timotei-iosif/proiect-tsc/Hardware/tsc.sch

## EAGLE design Hardware/tsc.sch (2026-04-10)

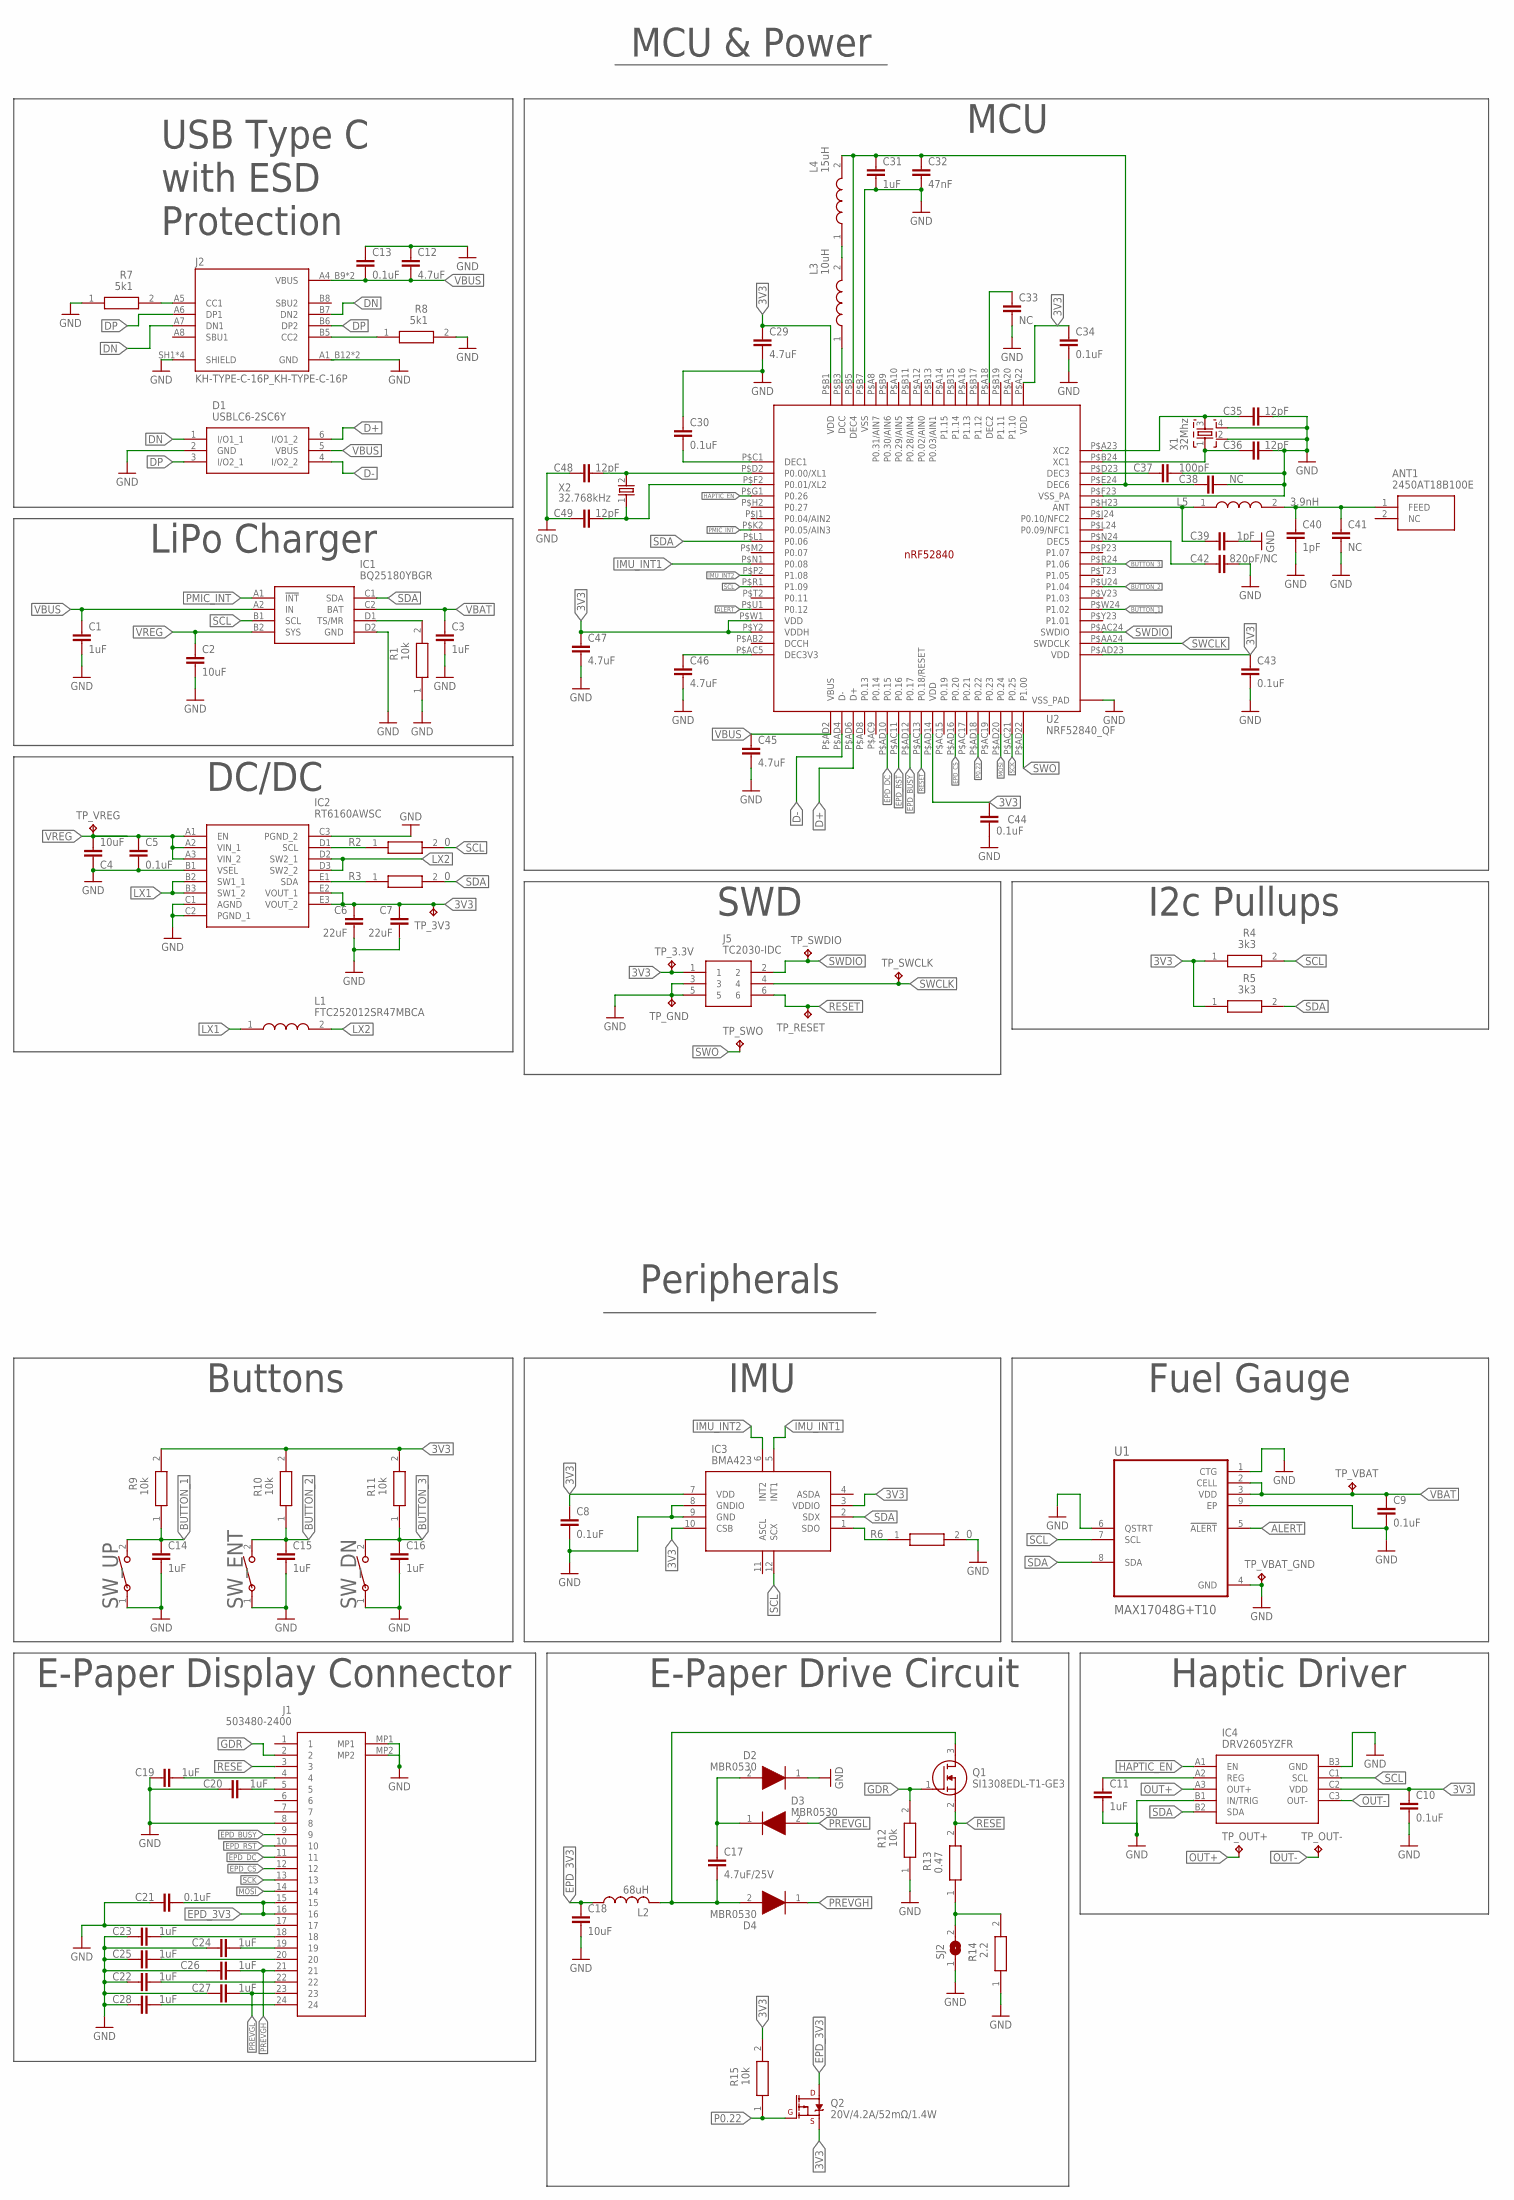
[picture p4: schematic tsc.sch]

Parts:
ANT1: 2450AT18B100E; 2450AT18B100E_ANTC3216X140N
C1, C3, C11, C14, C15, C16, C19, C20, C22, C23, C24, C25, C26, C27, C28, C31: 1uF; NORDIC_NRF_3_RESC0402_N
C2, C4, C18: 10uF; NORDIC_NRF_3_RESC0402_N
C5, C8, C9, C10, C13, C21, C30, C34, C43, C44: 0.1uF; NORDIC_NRF_3_RESC0201_N
C6, C7: 22uF; NORDIC_NRF_3_RESC0402_N
C12, C29, C45, C46, C47: 4.7uF; NORDIC_NRF_3_RESC0402_N
C17: 4.7uF/25V; NORDIC_NRF_3_RESC0402_N
C32: 47nF; NORDIC_NRF_3_RESC0201_N
C33, C38, C41: NC; NORDIC_NRF_3_RESC0201_N
C35, C36, C48, C49: 12pF; NORDIC_NRF_3_RESC0201_N
C37: 100pF; NORDIC_NRF_3_RESC0201_N
C39, C40: 1pF; NORDIC_NRF_3_RESC0201_N
C42: 820pF/NC; NORDIC_NRF_3_RESC0201_N
D1: USBLC6-2SC6Y; ESP32_C6_LIBRARY_3_SOT95P280X145-6N
D2, D3, D4: MBR0530; ESP32_C6_LIBRARY_5_SOD3716X135N
IC1: BQ25180YBGR; BQ25180YBGR_BGA8C40P2X4_100X155X50
IC2: RT6160AWSC; RT6160AWSC_BGA15C40P3X5_140X230X60
IC3: BMA423; BMA423_BMA423
IC4: DRV2605YZFR; DRV2605YZFR_BGA9C50P3X3_144X144X62
J1: 503480-2400; 503480-2400_5034802400
J2: KH-TYPE-C-16P_KH-TYPE-C-16P; KH-TYPE-C-16P_KINGHELM_KH-TYPE-C-16P
J5: TC2030-IDC; TC2030-IDC_TC2030IDC
L1: FTC252012SR47MBCA; MLP2016SR47MT0S1_INDC2016X100N
L2: 68uH; NORDIC_NRF_2_RESC0402_L
L3: 10uH; MLP2016SR47MT0S1_INDC2016X100N
L4: 15uH; MLP2016SR47MT0S1_INDC2016X100N
L5: 3.9nH; MLP2016SR47MT0S1_INDC2016X100N
Q1: SI1308EDL-T1-GE3; ESP32_C6_LIBRARY_6_SOT65P210X110-3N
Q2: 20V/4.2A/52mΩ/1.4W; ESP32_C6_LIBRARY_4_ESP32_C6_LIBRARY_4_ESP32_C6_LIBRARY_4_ES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
R1, R9, R10, R11, R12, R15: 10k; CPF0201D7K68C1_0201
R2, R3, R6: 0; CPF0201D7K68C1_0201
R4, R5: 3k3; CPF0201D7K68C1_0201
R7, R8: 5k1; CPF0201D7K68C1_0201
R13: 0.47; CPF0201D7K68C1_0201
R14: 2.2; CPF0201D7K68C1_0201
SJ2: -; ESP32_C6_LIBRARY_7_JUMPER_SJ
SW_DN: 2025-10-22_07-23-44_LIBRARY_EVP-AKE31ASW_EVP-AKE3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; 2025-10-22_07-23-44_LIBRARY_SW_EVP-AKE31A_PAN
SW_ENT: 2025-10-22_07-23-44_LIBRARY_EVP-AKE31ASW_EVP-AKE3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; 2025-10-22_07-23-44_LIBRARY_SW_EVP-AKE31A_PAN
SW_UP: 2025-10-22_07-23-44_LIBRARY_EVP-AKE31ASW_EVP-AKE3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; 2025-10-22_07-23-44_LIBRARY_SW_EVP-AKE31A_PAN
TP_3.3V, TP_3V3: HECTOR_WATCH_1_TPTP20R; HECTOR_WATCH_1_TP20R
TP_GND: HECTOR_WATCH_1_TPTP20R; HECTOR_WATCH_1_TP20R
TP_OUT+: HECTOR_WATCH_1_TPTP20R; HECTOR_WATCH_1_TP20R
TP_OUT-: HECTOR_WATCH_1_TPTP20R; HECTOR_WATCH_1_TP20R
TP_RESET: HECTOR_WATCH_1_TPTP20R; HECTOR_WATCH_1_TP20R
TP_SWCLK: HECTOR_WATCH_1_TPTP20R; HECTOR_WATCH_1_TP20R
TP_SWDIO: HECTOR_WATCH_1_TPTP20R; HECTOR_WATCH_1_TP20R
TP_SWO: HECTOR_WATCH_1_TPTP20R; HECTOR_WATCH_1_TP20R
TP_VBAT: HECTOR_WATCH_1_TPTP20R; HECTOR_WATCH_1_TP20R
TP_VBAT_GND: HECTOR_WATCH_1_TPTP20R; HECTOR_WATCH_1_TP20R
TP_VREG: HECTOR_WATCH_1_TPTP20R; HECTOR_WATCH_1_TP20R
U1: MAX17048G+T10; ESP32_C6_LIBRARY_SON50P200X200X80-9N
U2: NRF52840_QF; NORDIC_NRF_4_AQFN50P700X700X85_HS-74N
X1: 32Mhz; NORDIC_NRF_BT-XTAL_2016_N
X2: 32.768kHz; NORDIC_NRF_1_XTAL_3215_N

Connections:
3V3: C6.1, C7.1, C8.1, C10.1, C29.1, C34.1, C43.1, C44.1, C47.1, IC2.E2 (VOUT_1), IC2.E3 (VOUT_2), IC3.3 (VDDIO), IC3.7 (VDD), IC3.10 (CSB), IC4.C2 (VDD), J5.1, Q2.2 (S), R4.1, R5.1, R9.2, R10.2, R11.2, R15.2, TP_3.3V.TP, TP_3V3.TP, U2.P$A22 (VDD), U2.P$AD14 (VDD), U2.P$AD23 (VDD), U2.P$B1 (VDD), U2.P$W1 (VDD), U2.P$Y2 (VDDH)
ALERT: U1.5 (!ALERT), U2.P$U1 (P0.12)
BUTTON_1: C14.1, R9.1, SW_UP.2, U2.P$W24 (P1.02)
BUTTON_2: C15.1, R10.1, SW_ENT.2, U2.P$U24 (P1.04)
BUTTON_3: C16.1, R11.1, SW_DN.2, U2.P$R24 (P1.06)
D+: D1.6 (I/O1_2), U2.P$AD6 (D+)
D-: D1.4 (I/O2_2), U2.P$AD4 (D-)
DN: D1.1 (I/O1_1), J2.A7 (DN1), J2.B7 (DN2)
DP: D1.3 (I/O2_1), J2.A6 (DP1), J2.B6 (DP2)
EPD_3V3: C18.1, C21.2, J1.15, J1.16, L2.1, Q2.3 (D)
EPD_BUSY: J1.9, U2.P$AD12 (P0.17)
EPD_CS: J1.12, U2.P$AD16 (P0.20)
EPD_DC: J1.11, U2.P$AD10 (P0.15)
EPD_RST: J1.10, U2.P$AC11 (P0.16)
GDR: J1.2, Q1.1 (G), R12.2
GND: C1.2, C2.2, C3.2, C4.1, C5.2, C6.2, C7.2, C8.2, C9.2, C10.2, C11.2, C12.1, C13.1, C14.2, C15.2, C16.2, C18.2, C19.1, C20.1, C21.1, C22.1, C23.1, C24.1, C25.1, C26.1, C27.1, C28.1, C29.2, C30.1, C31.2, C32.2, C33.2, C34.2, C35.2, C36.2, C37.2, C38.2, C39.2, C40.2, C41.2, C42.2, C43.2, C44.2, C45.2, C46.2, C47.2, C48.1, C49.1, D1.2 (GND), D2.1 (K), IC1.D2 (GND), IC2.B1 (VSEL), IC2.C1 (AGND), IC2.C2 (PGND_1), IC2.C3 (PGND_2), IC3.8 (GNDIO), IC3.9 (GND), IC4.B1 (IN/TRIG), IC4.B3 (GND), J1.8, J1.17, J1.MP1, J1.MP2, J2.A1_B12 (GND), J2.SH1 (SHIELD), J5.3, J5.5, R1.1, R6.2, R7.1, R8.2, R12.1, R14.1, SJ2.1, SW_DN.1, SW_ENT.1, SW_UP.1, TP_GND.TP, TP_VBAT_GND.TP, U1.1 (CTG), U1.4 (GND), U1.6 (QSTRT), U1.9 (EP), U2.P$74 (VSS_PAD), U2.P$B7 (VSS), U2.P$F23 (VSS_PA), X1.2, X1.4
HAPTIC_EN: IC4.A1 (EN), U2.P$G1 (P0.26)
IMU_INT1: IC3.5 (INT1), U2.P$N1 (P0.08)
IMU_INT2: IC3.6 (INT2), U2.P$P2 (P1.08)
LX1: IC2.B2 (SW1_1), IC2.B3 (SW1_2), L1.1
LX2: IC2.D2 (SW2_1), IC2.D3 (SW2_2), L1.2
MOSI: J1.14, U2.P$AD20 (P0.24)
unnamed: IC1.D1 (TS/MR), R1.2
unnamed: IC2.D1 (SCL), R2.1
unnamed: IC2.E1 (SDA), R3.1
unnamed: IC3.1 (SDO), R6.1
unnamed: C11.1, IC4.A2 (REG)
unnamed: J2.A5 (CC1), R7.2
unnamed: C17.1, D2.2 (A), D3.1 (K)
unnamed: J2.B5 (CC2), R8.1
unnamed: C17.2, D4.2 (A), L2.2, Q1.3 (D)
unnamed: R13.1, R14.2, SJ2.2
unnamed: C19.2, J1.4
unnamed: C20.2, J1.5
unnamed: C23.2, J1.18
unnamed: C24.2, J1.19
unnamed: C25.2, J1.20
unnamed: C22.2, J1.22
unnamed: C28.2, J1.24
unnamed: C30.2, U2.P$C1 (DEC1)
unnamed: L3.1, U2.P$B3 (DCC)
unnamed: L3.2, L4.1
unnamed: C31.1, C32.1, C38.1, L4.2, U2.P$B5 (DEC4), U2.P$E24 (DEC6)
unnamed: C33.1, U2.P$A18 (DEC2)
unnamed: C36.1, U2.P$B24 (XC1), X1.1
unnamed: C35.1, U2.P$A23 (XC2), X1.3
unnamed: C37.1, U2.P$D23 (DEC3)
unnamed: C39.1, L5.1, U2.P$H23 (ANT)
unnamed: ANT1.1 (FEED), C40.1, C41.1, L5.2
unnamed: C42.1, U2.P$N24 (DEC5)
unnamed: C46.1, U2.P$AC5 (DEC3V3)
unnamed: C48.2, U2.P$D2 (P0.00/XL1), X2.2
unnamed: C49.2, U2.P$F2 (P0.01/XL2), X2.1
OUT+: IC4.A3 (OUT+), TP_OUT+.TP
OUT-: IC4.C3 (OUT-), TP_OUT-.TP
P0.22: Q2.1 (G), R15.1, U2.P$AD18 (P0.22)
PMIC_INT: IC1.A1 (!INT), U2.P$K2 (P0.05/AIN3)
PREVGH: C26.2, D4.1 (K), J1.21
PREVGL: C27.2, D3.2 (A), J1.23
RESE: J1.3, Q1.2 (S), R13.2
RESET: J5.6, TP_RESET.TP, U2.P$AC13 (P0.18/RESET)
SCK: J1.13, U2.P$AC21 (P0.25)
SCL: IC1.B1 (SCL), IC3.12 (SCX), IC4.C1 (SCL), R2.2, R4.2, U1.7 (SCL), U2.P$R1 (P1.09)
SDA: IC1.C1 (SDA), IC3.2 (SDX), IC4.B2 (SDA), R3.2, R5.2, U1.8 (SDA), U2.P$L1 (P0.06)
SWCLK: J5.4, TP_SWCLK.TP, U2.P$AA24 (SWDCLK)
SWDIO: J5.2, TP_SWDIO.TP, U2.P$AC24 (SWDIO)
SWO: TP_SWO.TP, U2.P$AD22 (P1.00)
VBAT: C3.1, C9.1, IC1.C2 (BAT), TP_VBAT.TP, U1.2 (CELL), U1.3 (VDD)
VBUS: C1.1, C12.2, C13.2, C45.1, D1.5 (VBUS), IC1.A2 (IN), J2.A4_B9 (VBUS), U2.P$AD2 (VBUS)
VREG: C2.1, C4.2, C5.1, IC1.B2 (SYS), IC2.A1 (EN), IC2.A2 (VIN_1), IC2.A3 (VIN_2), TP_VREG.TP

Notes on the sheet:
LiPo Charger
DC/DC
SWD
IMU
Fuel Gauge
Haptic Driver
USB Type C with ESD Protection
Buttons
E-Paper Drive Circuit
E-Paper Display Connector
MCU
I2c Pullups
MCU & Power
Peripherals
